oSkrobuk/infiniti-qx50-j55-monitoring/src/AlertManager.cpp

#include "AlertManager.h"

#include <LittleFS.h>

#include "BuzzerController.h"
#include "FsUtils.h"

// Бузер объявлен в main.cpp — используем extern для доступа без циклических зависимостей
extern BuzzerController buzzer;

// Глобальный объект
AlertManager alert_manager;

// Статические описания всех проверок (не изменяются в рантайме)
// Поля: code, name, display_name, description,
//        param1_label, param2_label, param3_label,
//        param1_def, param2_def, param3_def
const CheckDef AlertManager::CHECK_DEFS[AlertManager::CHECK_COUNT] = {
    {
        "E01",
        "Engine Oil Temp High",
        "ENGINE OIL\nTemperature\nHIGH",
        "Температура масла двигателя превысила максимальный порог",
        "Макс. темп, C", nullptr, nullptr,
        98.0f, 0.0f, 0.0f
    },
    {
        "E02",
        "Engine Coolant Temp High",
        "ENGINE COOLANT\nTemperature\nHIGH",
        "Температура антифриза двигателя превысила максимальный порог",
        "Макс. темп, C", nullptr, nullptr,
        96.0f, 0.0f, 0.0f
    },
    {
        "E03",
        "Radiator Coolant Temp High",
        "RADIATOR\nTemperature\nHIGH",
        "Температура антифриза радиатора превысила максимальный порог",
        "Макс. темп, C", nullptr, nullptr,
        90.0f, 0.0f, 0.0f
    },
    {
        "E04",
        "CVT Oil Temp High",
        "CVT OIL\nTemperature\nHIGH",
        "Температура масла вариатора превысила максимальный порог",
        "Макс. темп, C", nullptr, nullptr,
        100.0f, 0.0f, 0.0f
    },
    {
        "E05",
        "Engine RPM Overspeed",
        "ENGINE\nRPM\nOVERSPEED",
        "Обороты двигателя превысили максимально допустимый предел",
        "Макс. об/мин", nullptr, nullptr,
        6500.0f, 0.0f, 0.0f
    },
    {
        "E06",
        "Battery Voltage Low",
        "BATTERY\nVoltage\nLOW",
        "Напряжение бортовой сети упало ниже минимального порога",
        "Мин. напряж, В", nullptr, nullptr,
        11.5f, 0.0f, 0.0f
    },
    {
        "E07",
        "Battery Voltage High",
        "BATTERY\nVoltage\nHIGH",
        "Напряжение бортовой сети превысило максимальный порог",
        "Макс. напряж, В", nullptr, nullptr,
        15.0f, 0.0f, 0.0f
    },
    {
        "E08",
        "Oil Pressure Low",
        "OIL\nPressure\nLOW",
        "Напряжение датчика давления масла ниже нормы для текущих оборотов",
        "Порог об/мин", "Мин. В (низк. об)", "Мин. В (выс. об)",
        3000.0f, 1.4f, 2.9f
    },
    {
        "E09",
        "Oil-Coolant Temp Delta High",
        "OIL vs COOLANT\nDelta\nHIGH",
        "Разница температур масла и антифриза двигателя превысила допустимый порог",
        "Макс. дельта, C", nullptr, nullptr,
        14.0f, 0.0f, 0.0f
    },
};

// Прочитать тайминг из JSON: число в миллисекундах, зажатое в допустимые границы.
// Если поля нет или это не число — возвращается fallback
static uint32_t read_timing_ms(JsonVariantConst value, uint32_t fallback, uint32_t lo, uint32_t hi)
{
    if (!value.is<float>()) return fallback;

    float ms = value.as<float>();
    if (ms < 0.0f) ms = 0.0f;

    uint32_t rounded = static_cast<uint32_t>(ms + 0.5f);
    if (rounded < lo) return lo;
    if (rounded > hi) return hi;
    return rounded;
}

// ─────────────────────────────────────────────────────────────────────────────

AlertManager::AlertManager()
    : log_count_(0), active_since_(0)
{
    active_code_[0]  = '\0';
    active_desc_[0]  = '\0';
    active_dname_[0] = '\0';
    apply_check_defaults_();
    memset(last_trigger_ms_, 0, sizeof(last_trigger_ms_));
    memset(pending_since_, 0, sizeof(pending_since_));
    memset(pending_active_, 0, sizeof(pending_active_));
    memset(log_, 0, sizeof(log_));
}

void AlertManager::apply_check_defaults_()
{
    confirm_ms_   = ALERT_CONFIRM_MS_DEF;
    retrigger_ms_ = ALERT_RETRIGGER_MS_DEF;

    for (uint8_t i = 0; i < CHECK_COUNT; ++i) {
        checks_[i].enabled = true;
        checks_[i].param1  = CHECK_DEFS[i].param1_def;
        checks_[i].param2  = CHECK_DEFS[i].param2_def;
        checks_[i].param3  = CHECK_DEFS[i].param3_def;
    }
}

bool AlertManager::init()
{
    // LittleFS уже смонтирован в config.init() — вызываем только загрузку файлов
    bool missing = false;
    load_checks_(missing);

    // Перезаписываем файл только если он отсутствует, повреждён или неполный
    // (например, после обновления прошивки появилась новая проверка E09)
    if (missing) {
        save_checks_();
    }

    load_log_();
    Serial.println("[Alert] AlertManager инициализирован");
    return true;
}

// ─────────────────────────────────────────────────────────────────────────────
// Основная функция проверки — вызывается каждые 200 мс.
//
// Условие каждой проверки вычисляется целиком, вместе с проверкой наличия
// данных: если по метрике нет кадров, условие считается ложным и отсчет
// подтверждения в try_trigger_ обнуляется

void AlertManager::update(const CanMetrics &m)
{
    // E01: температура масла ДВС выше максимума
    try_trigger_(0, m.engine_oil_ts != 0 && m.engine_oil > checks_[0].param1);

    // E02: температура ОЖ ДВС выше максимума
    try_trigger_(1, m.engine_coolant_ts != 0 && m.engine_coolant > checks_[1].param1);

    // E03: температура ОЖ радиатора выше максимума
    try_trigger_(2, m.radiator_coolant_ts != 0 && m.radiator_coolant > checks_[2].param1);

    // E04: температура масла вариатора выше максимума
    try_trigger_(3, m.cvt_temp_ts != 0 && m.cvt_temp > checks_[3].param1);

    // E05: обороты выше максимума
    try_trigger_(4, m.engine_rpm_ts != 0 && m.engine_rpm > checks_[4].param1);

    // E06: напряжение бортовой сети ниже минимума
    try_trigger_(5, m.battery_voltage_ts != 0 && m.battery_voltage < checks_[5].param1);

    // E07: напряжение бортовой сети выше максимума
    try_trigger_(6, m.battery_voltage_ts != 0 && m.battery_voltage > checks_[6].param1);

    // E08: давление масла (напряжение датчика) ниже нормы для текущих оборотов
    // При оборотах == 0 (двигатель заглушен) проверку не выполняем
    bool oil_pressure_low = false;
    if (m.oil_pressure_volt_ts != 0 && m.engine_rpm_ts != 0 && m.engine_rpm != 0.0f) {
        float min_volt = (m.engine_rpm < checks_[7].param1)
            ? checks_[7].param2
            : checks_[7].param3;
        oil_pressure_low = m.oil_pressure_volt < min_volt;
    }
    try_trigger_(7, oil_pressure_low);

    // E09: разница температур масла и антифриза ДВС выше порога
    bool delta_high = false;
    if (m.engine_oil_ts != 0 && m.engine_coolant_ts != 0) {
        delta_high = (m.engine_oil - m.engine_coolant) > checks_[8].param1;
    }
    try_trigger_(8, delta_high);
}

int16_t AlertManager::find_log_index_(const char *code) const
{
    for (uint8_t i = 0; i < log_count_; ++i) {
        if (strncmp(log_[i].code, code, sizeof(log_[0].code)) == 0) {
            return static_cast<int16_t>(i);
        }
    }
    return -1;
}

void AlertManager::try_trigger_(uint8_t idx, bool triggered)
{
    uint32_t now = millis();

    if (!triggered) {
        // Условие снялось — следующий выход за диапазон начнет отсчет заново
        pending_active_[idx] = false;
        return;
    }

    // Первый выход за диапазон: запоминаем момент и ждем подтверждения
    if (!pending_active_[idx]) {
        pending_active_[idx] = true;
        pending_since_[idx]  = now;
    }

    // Показание, выскочившее за диапазон на доли секунды, алертом не считаем:
    // условие должно продержаться не меньше confirm_ms_ (при нуле алертим сразу)
    if ((now - pending_since_[idx]) < confirm_ms_) return;

    // Запись журнала ищем заранее: в однократном режиме именно ее наличие,
    // а не флаг сессии, запрещает повторное срабатывание
    int16_t log_idx = find_log_index_(CHECK_DEFS[idx].code);

    if (checks_[idx].enabled) {
        // Режим повтора: антидребезг — не повторять чаще retrigger_ms_
        if (last_trigger_ms_[idx] != 0 &&
            (now - last_trigger_ms_[idx]) < retrigger_ms_) {
            return;
        }
    } else {
        // Однократный режим: алертим, только пока кода нет в журнале.
        // Признак «уже показывали» — сама запись в памяти, поэтому очистка
        // журнала из Web UI снова разрешает алерт, не дожидаясь перезагрузки МК
        if (log_idx >= 0) return;
    }

    last_trigger_ms_[idx] = now;
    active_since_          = now;
    strncpy(active_code_,  CHECK_DEFS[idx].code,         sizeof(active_code_) - 1);
    strncpy(active_desc_,  CHECK_DEFS[idx].description,  sizeof(active_desc_) - 1);
    strncpy(active_dname_, CHECK_DEFS[idx].display_name, sizeof(active_dname_) - 1);
    active_code_[sizeof(active_code_) - 1]   = '\0';
    active_desc_[sizeof(active_desc_) - 1]   = '\0';
    active_dname_[sizeof(active_dname_) - 1] = '\0';

    // Сигнал бузером
    buzzer.trigger_alert();

    // Логируем: запись с этим кодом уже нашли выше
    if (log_idx >= 0) {
        log_[log_idx].count++;
    } else if (log_count_ < ALERT_LOG_MAX) {
        strncpy(log_[log_count_].code,        CHECK_DEFS[idx].code,        sizeof(log_[0].code) - 1);
        strncpy(log_[log_count_].description, CHECK_DEFS[idx].description, sizeof(log_[0].description) - 1);
        log_[log_count_].code[sizeof(log_[0].code) - 1]               = '\0';
        log_[log_count_].description[sizeof(log_[0].description) - 1] = '\0';
        log_[log_count_].count = 1;
        log_count_++;
    }

    save_log_();

    Serial.printf("[Alert] Сработала проверка %s: %s\r\n",
                  CHECK_DEFS[idx].code, CHECK_DEFS[idx].description);
}

// ─────────────────────────────────────────────────────────────────────────────
// Запросы состояния активного алерта

bool AlertManager::has_active_alert() const
{
    if (active_code_[0] == '\0') return false;
    return (millis() - active_since_) < ALERT_DISPLAY_MS;
}

const char *AlertManager::active_code() const
{
    return active_code_;
}

const char *AlertManager::active_description() const
{
    return active_desc_;
}

const char *AlertManager::active_display_name() const
{
    return active_dname_;
}

// ─────────────────────────────────────────────────────────────────────────────
// Сериализация для Web API

String AlertManager::log_to_json() const
{
    JsonDocument doc;
    JsonArray arr = doc.to<JsonArray>();

    for (uint8_t i = 0; i < log_count_; ++i) {
        JsonObject obj = arr.add<JsonObject>();
        obj["code"]        = log_[i].code;
        obj["description"] = log_[i].description;
        obj["count"]       = log_[i].count;
    }

    String out;
    serializeJson(doc, out);
    return out;
}

bool AlertManager::clear_log()
{
    memset(log_, 0, sizeof(log_));
    log_count_ = 0;
    active_code_[0]  = '\0';
    active_desc_[0]  = '\0';
    active_dname_[0] = '\0';

    // Сбрасываем и антидребезг: журнал пуст, значит ни одна проверка больше
    // не считается показанной — при сохраняющейся неисправности алерт
    // поднимется заново в обоих режимах
    memset(last_trigger_ms_, 0, sizeof(last_trigger_ms_));

    // Удаляем файл журнала (remove() безопасен если файла нет)
    LittleFS.remove(ALERTS_LOG_FILE);

    Serial.println("[Alert] Журнал алертов очищен");
    return true;
}

String AlertManager::checks_to_json() const
{
    JsonDocument doc;

    doc[CHECKS_TIMING_KEY]["confirm_ms"]   = confirm_ms_;
    doc[CHECKS_TIMING_KEY]["retrigger_ms"] = retrigger_ms_;

    for (uint8_t i = 0; i < CHECK_COUNT; ++i) {
        const char *code     = CHECK_DEFS[i].code;
        doc[code]["enabled"] = checks_[i].enabled;
        doc[code]["param1"]  = checks_[i].param1;
        doc[code]["param2"]  = checks_[i].param2;
        doc[code]["param3"]  = checks_[i].param3;
    }

    String out;
    serializeJson(doc, out);
    return out;
}

bool AlertManager::checks_from_json(const String &json)
{
    JsonDocument doc;
    DeserializationError err = deserializeJson(doc, json);
    if (err) {
        Serial.printf("[Alert] ОШИБКА парсинга JSON проверок: %s\r\n", err.c_str());
        return false;
    }

    if (doc[CHECKS_TIMING_KEY].is<JsonObject>()) {
        JsonObjectConst timing = doc[CHECKS_TIMING_KEY].as<JsonObjectConst>();
        confirm_ms_   = read_timing_ms(timing["confirm_ms"], confirm_ms_,
                                       ALERT_CONFIRM_MS_MIN, ALERT_CONFIRM_MS_MAX);
        retrigger_ms_ = read_timing_ms(timing["retrigger_ms"], retrigger_ms_,
                                       ALERT_RETRIGGER_MS_MIN, ALERT_RETRIGGER_MS_MAX);
    }

    for (uint8_t i = 0; i < CHECK_COUNT; ++i) {
        const char *code = CHECK_DEFS[i].code;
        if (doc[code].is<JsonObject>()) {
            JsonObjectConst obj = doc[code].as<JsonObjectConst>();
            if (obj["enabled"].is<bool>()) checks_[i].enabled = obj["enabled"].as<bool>();
            if (obj["param1"].is<float>()) checks_[i].param1  = obj["param1"].as<float>();
            if (obj["param2"].is<float>()) checks_[i].param2  = obj["param2"].as<float>();
            if (obj["param3"].is<float>()) checks_[i].param3  = obj["param3"].as<float>();
        }
    }

    return save_checks_();
}

// ─────────────────────────────────────────────────────────────────────────────
// Персистентность

bool AlertManager::load_checks_(bool &missing)
{
    missing = false;

    if (!LittleFS.exists(CHECKS_CONFIG_FILE)) {
        Serial.println("[Alert] Файл проверок не найден, используем значения по умолчанию");
        missing = true;
        return true;
    }

    File f = LittleFS.open(CHECKS_CONFIG_FILE, "r");
    if (!f) {
        Serial.println("[Alert] ОШИБКА: не удалось открыть файл проверок");
        return false;
    }

    JsonDocument doc;
    DeserializationError err = deserializeJson(doc, f);
    f.close();

    if (err) {
        // Повреждённый файл — остаёмся на дефолтах и перезаписываем его
        Serial.printf("[Alert] ОШИБКА парсинга файла проверок: %s\r\n", err.c_str());
        missing = true;
        return false;
    }

    // Секция таймингов появилась позже проверок — в файле от старой прошивки
    // ее нет, поэтому дефолты дописываются туда так же, как новые проверки
    if (doc[CHECKS_TIMING_KEY].is<JsonObject>()) {
        JsonObjectConst timing = doc[CHECKS_TIMING_KEY].as<JsonObjectConst>();
        if (timing["confirm_ms"].is<float>()) {
            confirm_ms_ = read_timing_ms(timing["confirm_ms"], confirm_ms_,
                                         ALERT_CONFIRM_MS_MIN, ALERT_CONFIRM_MS_MAX);
        } else {
            missing = true;
        }
        if (timing["retrigger_ms"].is<float>()) {
            retrigger_ms_ = read_timing_ms(timing["retrigger_ms"], retrigger_ms_,
                                           ALERT_RETRIGGER_MS_MIN, ALERT_RETRIGGER_MS_MAX);
        } else {
            missing = true;
        }
    } else {
        missing = true;
    }

    for (uint8_t i = 0; i < CHECK_COUNT; ++i) {
        const char *code = CHECK_DEFS[i].code;
        if (!doc[code].is<JsonObject>()) {
            // Проверки нет в файле — например, E09 появилась после обновления прошивки
            missing = true;
            continue;
        }

        JsonObjectConst obj = doc[code].as<JsonObjectConst>();
        if (obj["enabled"].is<bool>())  checks_[i].enabled = obj["enabled"].as<bool>();  else missing = true;
        if (obj["param1"].is<float>())  checks_[i].param1  = obj["param1"].as<float>();  else missing = true;
        if (obj["param2"].is<float>())  checks_[i].param2  = obj["param2"].as<float>();  else missing = true;
        if (obj["param3"].is<float>())  checks_[i].param3  = obj["param3"].as<float>();  else missing = true;
    }

    Serial.println("[Alert] Конфиг проверок загружен");
    return true;
}

bool AlertManager::save_checks_()
{
    JsonDocument doc;

    doc[CHECKS_TIMING_KEY]["confirm_ms"]   = confirm_ms_;
    doc[CHECKS_TIMING_KEY]["retrigger_ms"] = retrigger_ms_;

    for (uint8_t i = 0; i < CHECK_COUNT; ++i) {
        const char *code     = CHECK_DEFS[i].code;
        doc[code]["enabled"] = checks_[i].enabled;
        doc[code]["param1"]  = checks_[i].param1;
        doc[code]["param2"]  = checks_[i].param2;
        doc[code]["param3"]  = checks_[i].param3;
    }

    // Пишем атомарно: при пропадании питания прежний файл останется целым
    if (!fs_write_json_atomic(CHECKS_CONFIG_FILE, doc)) {
        Serial.println("[Alert] ОШИБКА: не удалось сохранить конфиг проверок");
        return false;
    }

    Serial.println("[Alert] Конфиг проверок сохранён");
    return true;
}

bool AlertManager::load_log_()
{
    // Если файла нет — это нормальная ситуация (первый запуск или после очистки)
    if (!LittleFS.exists(ALERTS_LOG_FILE)) {
        Serial.println("[Alert] Файл журнала не найден, журнал пуст");
        return true;
    }

    File f = LittleFS.open(ALERTS_LOG_FILE, "r");
    if (!f) {
        // Файл недоступен — считаем журнал пустым, не возвращаем ошибку
        Serial.println("[Alert] Файл журнала недоступен, журнал пуст");
        return true;
    }

    JsonDocument doc;
    DeserializationError err = deserializeJson(doc, f);
    f.close();

    if (err) {
        // Повреждённый файл — считаем журнал пустым
        Serial.printf("[Alert] Файл журнала повреждён (%s), журнал пуст\r\n", err.c_str());
        LittleFS.remove(ALERTS_LOG_FILE);
        return true;
    }

    JsonArrayConst arr = doc.as<JsonArrayConst>();
    log_count_ = 0;
    for (JsonObjectConst obj : arr) {
        if (log_count_ >= ALERT_LOG_MAX) break;
        const char *code = obj["code"] | "";
        const char *desc = obj["description"] | "";
        uint32_t count   = obj["count"] | 1u;
        strncpy(log_[log_count_].code,        code, sizeof(log_[0].code) - 1);
        strncpy(log_[log_count_].description, desc, sizeof(log_[0].description) - 1);
        log_[log_count_].code[sizeof(log_[0].code) - 1]               = '\0';
        log_[log_count_].description[sizeof(log_[0].description) - 1] = '\0';
        log_[log_count_].count = count;
        log_count_++;
    }

    Serial.printf("[Alert] Журнал загружен: %u записей\r\n", log_count_);
    return true;
}

bool AlertManager::save_log_()
{
    JsonDocument doc;
    JsonArray arr = doc.to<JsonArray>();

    for (uint8_t i = 0; i < log_count_; ++i) {
        JsonObject obj = arr.add<JsonObject>();
        obj["code"]        = log_[i].code;
        obj["description"] = log_[i].description;
        obj["count"]       = log_[i].count;
    }

    // Пишем атомарно: журнал переживет пропадание питания в момент записи
    if (!fs_write_json_atomic(ALERTS_LOG_FILE, doc)) {
        Serial.println("[Alert] ОШИБКА: не удалось сохранить файл журнала");
        return false;
    }

    return true;
}
